01joja/project-mirror-E7020E/nuttali/examples/nuttali_buttons.rs

//! nuttali_buttons
//!
//! HAL OutputPin abstractions
//!
//! What it covers:
//! - using embedded hal, and the OutputPin abstraction

#![no_main]
#![no_std]


//use core::intrinsics::rotate_left;

use core::convert::TryInto;

use panic_rtt_target as _;
use rtic::cyccnt::{Instant, U32Ext as _};
use rtt_target::{rprint, rprintln, rtt_init_print};
use stm32f4xx_hal::{gpio::{AlternateOD, PullUp}, stm32};

use stm32f4xx_hal::{
    gpio::{
        gpioa::{
            PA1, PA2, PA3, PA4, PA5, PA6, PA7},
        gpiob::{
            PB14,PB15},
        gpioc::{
            PC4, PC5}, 
    Input, Output, PushPull, PullDown, Alternate},
    prelude::*,
};

use embedded_hal::digital::v2::{OutputPin, ToggleableOutputPin, InputPin};

const OFFSET: u32 = 50_000_000;

#[rtic::app(device = stm32f4xx_hal::stm32, monotonic = rtic::cyccnt::CYCCNT, peripherals = true)]
const APP: () = {
    struct Resources {
        // late resources
        //GPIOA: stm32::GPIOA,
        led_blue: PA1<Output<PushPull>>,
        led_red: PA3<Output<PushPull>>,
        led_green: PA2<Output<PushPull>>,
    
        turbo_button: PA4<Input<PullDown>>,
        right_button: PA5<Input<PullDown>>,
        scroll_button: PA6<Input<PullDown>>,

        scroll_forward: PC4<Input<PullDown>>,
        scroll_back: PA7<Input<PullDown>>,

        forward_button: PB14<Input<PullDown>>,
        backward_button: PB15<Input<PullDown>>,

        left_button: PC5<Input<PullDown>>,


    }
    //#[init(schedule = [toggle])]
    #[init(schedule = [is_button_pressed])]
    fn init(cx: init::Context) -> init::LateResources {
        rtt_init_print!();
        rprintln!("init");


        let mut core = cx.core;
        let device = cx.device;


        // Initialize (enable) the monotonic timer (CYCCNT)
        core.DCB.enable_trace();
        core.DWT.enable_cycle_counter();

        // semantically, the monotonic timer is frozen at time "zero" during `init`
        // NOTE do *not* call `Instant::now` in this context; it will return a nonsense value
        let now = cx.start; // the start time of the system

        // Schedule `toggle` to run 8e6 cycles (clock cycles) in the future
        //let number_of_toggles = 0;
        //cx.schedule.toggle(now + OFFSET.cycles(),number_of_toggles).unwrap();

        cx.schedule.is_button_pressed(now + OFFSET.cycles()).unwrap();

        
        //let left_button = gpioc.pc5.into_pull_up_input();
        //let left_button_timer = dp.TIM2;

        // power on GPIOA, RM0368 6.3.11
        //device.RCC.ahb1enr.modify(|_, w| w.gpioaen().set_bit());
        
        //device.RCC.ahb1enr.modify(|_, w| w.gpiocen().set_bit());
        //configure PA3 as output, RM0368 8.4.1
        device.GPIOA.moder.modify(|_, w| w.moder3().bits(1));
        device.GPIOA.moder.modify(|_, w| w.moder2().bits(1));
        device.GPIOA.moder.modify(|_, w| w.moder1().bits(1));

        device.GPIOC.moder.modify(|_, w| w.moder5().bits(1));
        //left_button_read = device.GPIOCEN_R;
        let gpioa = device.GPIOA.split();
        let gpiob = device.GPIOB.split();
        let gpioc = device.GPIOC.split();        
        
        // pass on late resources
        init::LateResources {
            //GPIOA: device.GPIOA,
            led_red: gpioa.pa3.into_push_pull_output(),
            led_green: gpioa.pa2.into_push_pull_output(),
            led_blue: gpioa.pa1.into_push_pull_output(),
            turbo_button: gpioa.pa4.into_pull_down_input(),
            left_button: gpioc.pc5.into_pull_down_input(),
            right_button: gpioa.pa5.into_pull_down_input(),

            scroll_forward: gpioc.pc4.into_pull_down_input(),
            scroll_button: gpioa.pa6.into_pull_down_input(),
            scroll_back: gpioa.pa7.into_pull_down_input(),

            forward_button: gpiob.pb14.into_pull_down_input(),
            backward_button: gpiob.pb15.into_pull_down_input(),
        }
    }

    #[idle]
    fn idle(_cx: idle::Context) -> ! {
        rprintln!("idle");
        loop {
            continue;
        }
    }

    #[task(resources = [left_button, right_button, scroll_button, turbo_button, forward_button, backward_button, 
        scroll_forward, scroll_back, led_red], schedule = [is_button_pressed])]
    fn is_button_pressed(cx: is_button_pressed::Context) {

        //[left,right,mouse,turbo,forward,backward]
        let mut buttons: [bool;8] = [false,false,false,false,false,false,false,false];

        let mut buttons_prev : [bool;8] = [false,false,false,false,false,false,false, false];
        loop {
            //cx.resources.left_button.set_high().ok();
            if cx.resources.left_button.is_high().unwrap() {
                buttons[0] = false;
                //rprintln!("left button is set high");
            } else {
                buttons[0] = true;
                //rprintln!("left button is set low");
            }

            if cx.resources.right_button.is_high().unwrap() {
                buttons[1] = false;
            } else {
                buttons[1] = true;
                //rprintln!("right button is set low");
            }
            
            if cx.resources.scroll_button.is_low().unwrap() {
                buttons[2] = false;
            
                
            } else {
                buttons[2] = true;
                //rprintln!("scroll button is set high");
            }

            if cx.resources.turbo_button.is_low().unwrap() {
                buttons[3] = false;
            } else {
                buttons[3] = true;
                //rprintln!("turbo/dpi button is set high");
            }
            if cx.resources.forward_button.is_low().unwrap(){

                buttons[4] = false;

            }
            else{
                buttons[4] = true;
            // rprintln!("forward button is set high");
            }

            if cx.resources.backward_button.is_low().unwrap(){
                buttons[5] = false
            }
            else{
                buttons[5] = true;
                //rprintln!("bacward button is set high");
            }

            if cx.resources.scroll_forward.is_high().unwrap(){
                buttons[6] = true
            } else {
                buttons[6] = false;
            }

            if cx.resources.scroll_back.is_high().unwrap(){
                buttons[7] = true
            } else {
                buttons[7] = false;
            }

            if buttons != buttons_prev{

                rprintln!("Buttons -- Right: {}, Left: {}, Middle: {}, DPI: {}, Fram: {}, Bak: {}, scroll forward: {}, scroll back: {}", buttons[0], buttons[1], buttons[2], buttons[3], 
                    buttons[4],buttons[5], buttons[6], buttons[7]);

                //rprintln!(print);
                buttons_prev = buttons;
            }


        }
    }

    extern "C" {
        fn EXTI0();
        fn USART1();
    }
};
